TychoRasch/ProjectMask/src/03 Carbon Dioxide Test/Parts/PARTReservoirAssembly.SLDASM

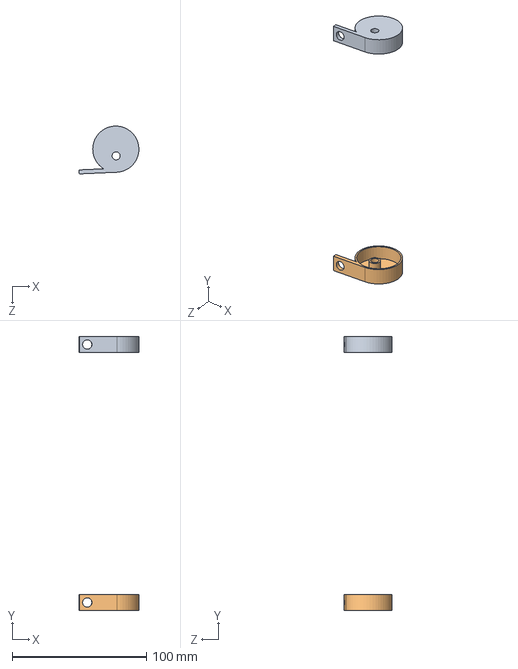
[picture p2: CAD file, 2020-04-27]
src/03 Carbon Dioxide Test/Parts/PARTReservoirAssembly.SLDASM
44.5 x 204.0 x 35.6 mm
PARTReservoirL
PARTReservoirR
