TychoRasch/ProjectMask/src/03 Carbon Dioxide Test/Parts/PARTVenturiAssembly.SLDASM

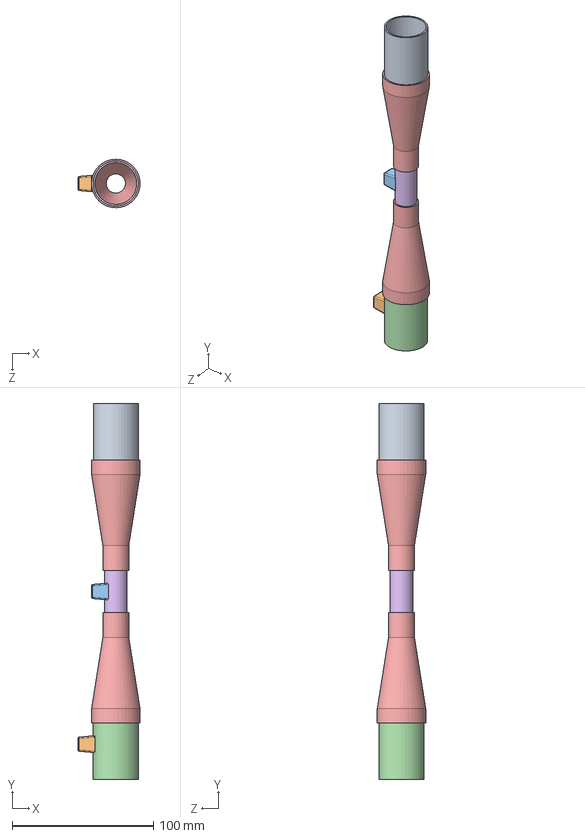
[picture p11: CAD file, 2020-04-27]
src/03 Carbon Dioxide Test/Parts/PARTVenturiAssembly.SLDASM
44.0 x 266.2 x 34.4 mm
PART16mm buis Venturi
PART32-16mm buis Venturi x 2
PART32mm buis Venturi
PART16mm Tube Connect Venturi
PART32mm Tube Connect Venturi
PART32mm buis
