TychoRasch/ProjectMask/src/04 Dry Particle Test/Particle test v1.1/Laser cut files/Baseplate v2.DXF

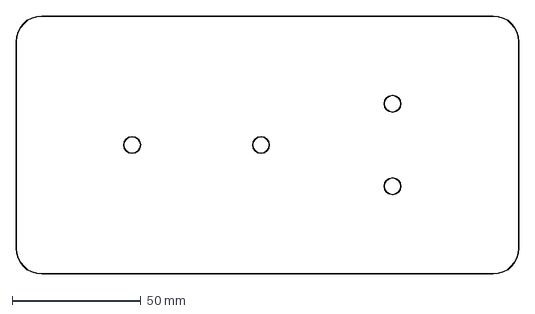
[picture p18: CAD file, 2020-04-27]
src/04 Dry Particle Test/Particle test v1.1/Laser cut files/Baseplate v2.DXF
195.0 x 100.0 mm
