TychoRasch/ProjectMask/src/04 Dry Particle Test/Particle test v1.1/Solidworks model/Baseplate v2.SLDPRT

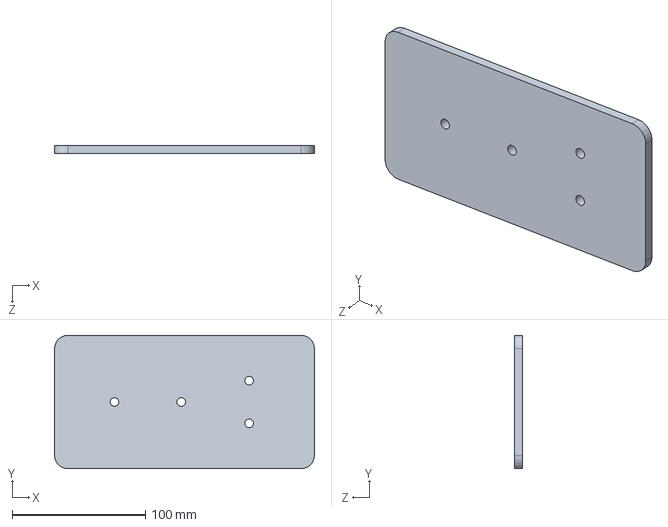
[picture p19: CAD file, 2020-04-27]
src/04 Dry Particle Test/Particle test v1.1/Solidworks model/Baseplate v2.SLDPRT
195.0 x 100.0 x 6.00 mm
