TychoRasch/ProjectMask/src/04 Dry Particle Test/Particle test v1.1/Solidworks model/Particle chamber v3.SLDPRT

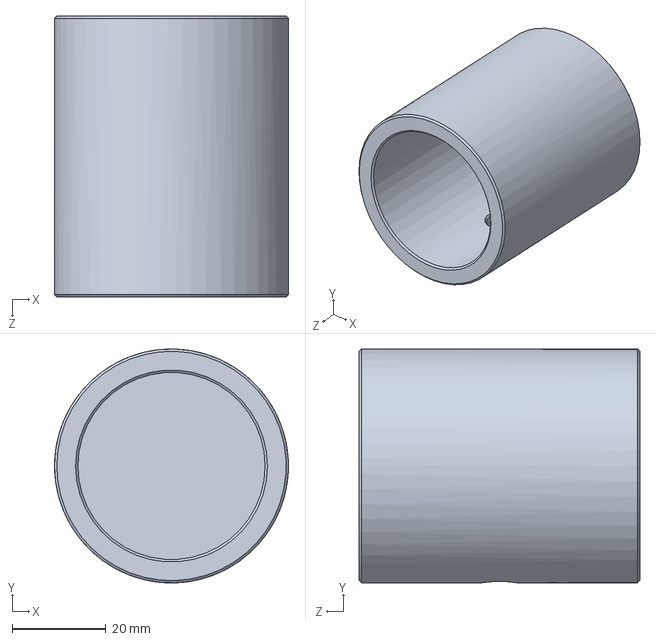
[picture p20: CAD file, 2020-04-27]
src/04 Dry Particle Test/Particle test v1.1/Solidworks model/Particle chamber v3.SLDPRT
50.0 x 50.0 x 60.0 mm
