TychoRasch/ProjectMask/src/03 Carbon Dioxide Test/Parts/PARTMounting1pipe.SLDPRT

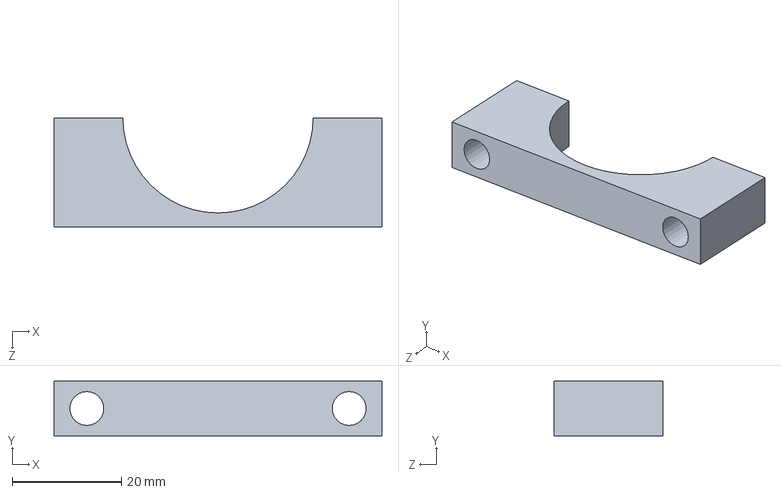
[picture p21: CAD file, 2020-04-27]
src/03 Carbon Dioxide Test/Parts/PARTMounting1pipe.SLDPRT
60.0 x 10.0 x 20.0 mm
