TychoRasch/ProjectMask/src/04 Dry Particle Test/Nebulizer/SolidworksNEN/Feed Tube.SLDPRT

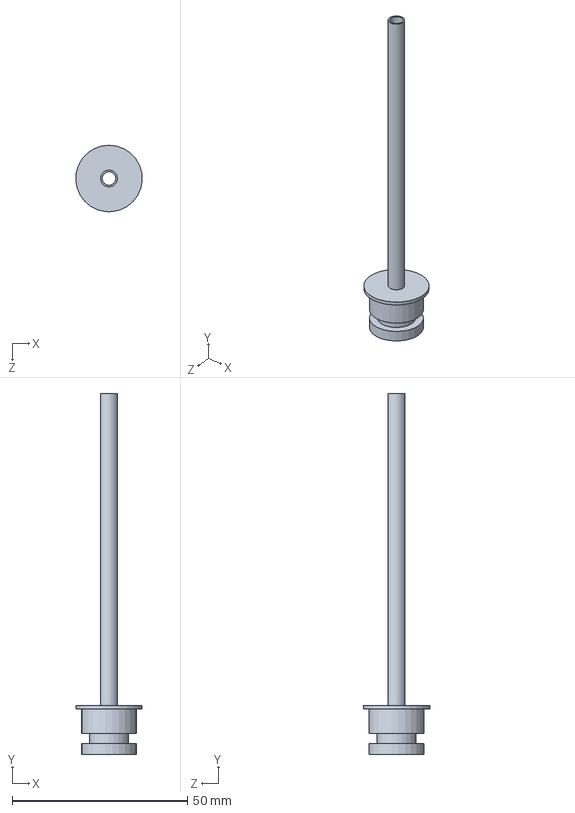
[picture p22: CAD file, 2020-04-27]
src/04 Dry Particle Test/Nebulizer/SolidworksNEN/Feed Tube.SLDPRT
19.0 x 103.0 x 19.0 mm
