TychoRasch/ProjectMask/src/04 Dry Particle Test/Particle test v1.1/Solidworks model/Lid container v3.SLDPRT

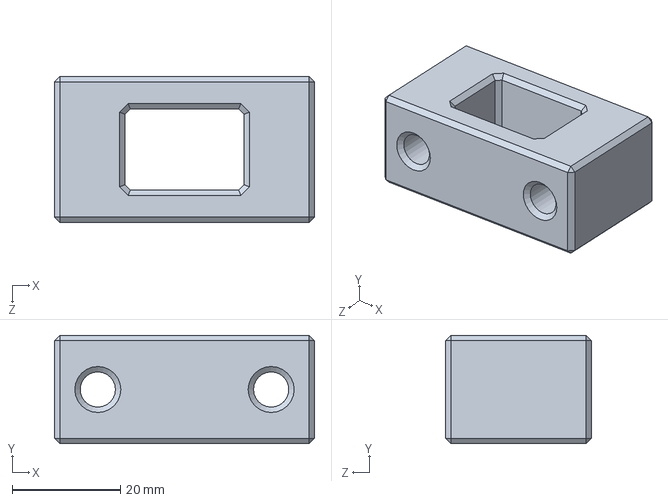
[picture p23: CAD file, 2020-04-27]
src/04 Dry Particle Test/Particle test v1.1/Solidworks model/Lid container v3.SLDPRT
48.0 x 20.0 x 27.0 mm
