TychoRasch/ProjectMask/src/03 Carbon Dioxide Test/Parts/PARTCO2Sensor.SLDPRT

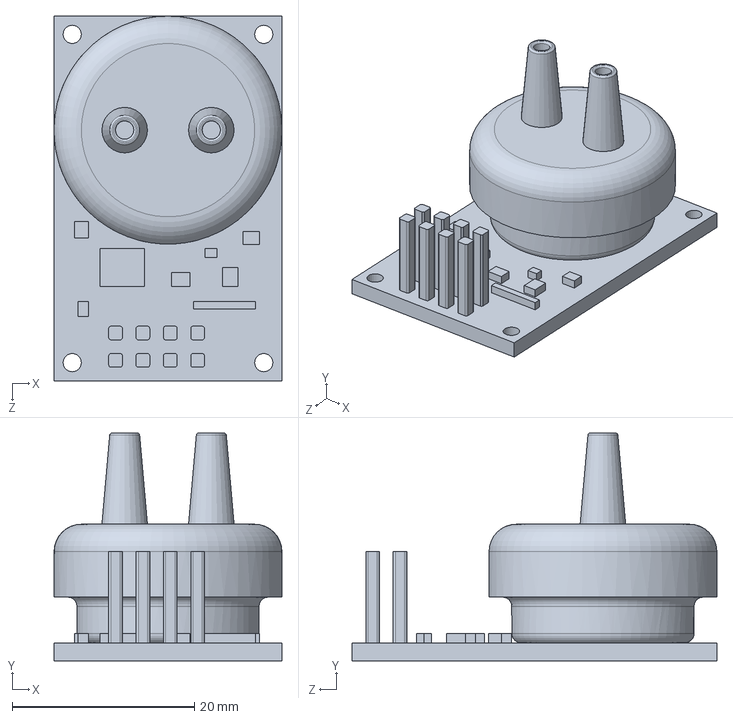
[picture p24: CAD file, 2020-04-27]
src/03 Carbon Dioxide Test/Parts/PARTCO2Sensor.SLDPRT
25.0 x 25.0 x 40.0 mm
