TychoRasch/ProjectMask/src/04 Dry Particle Test/Nebulizer/SolidworksNEN/Plug.SLDPRT

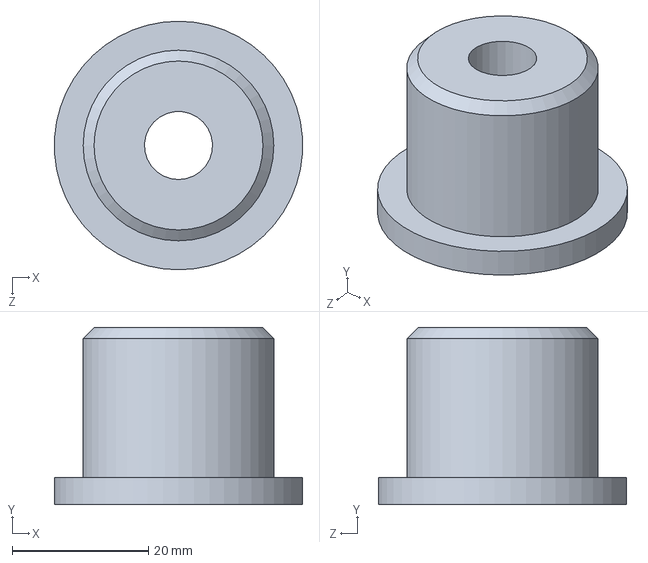
[picture p25: CAD file, 2020-04-27]
src/04 Dry Particle Test/Nebulizer/SolidworksNEN/Plug.SLDPRT
36.4 x 26.0 x 36.5 mm
