TychoRasch/ProjectMask/src/04 Dry Particle Test/Particle test v1.1/Solidworks model/Knob M6.SLDPRT

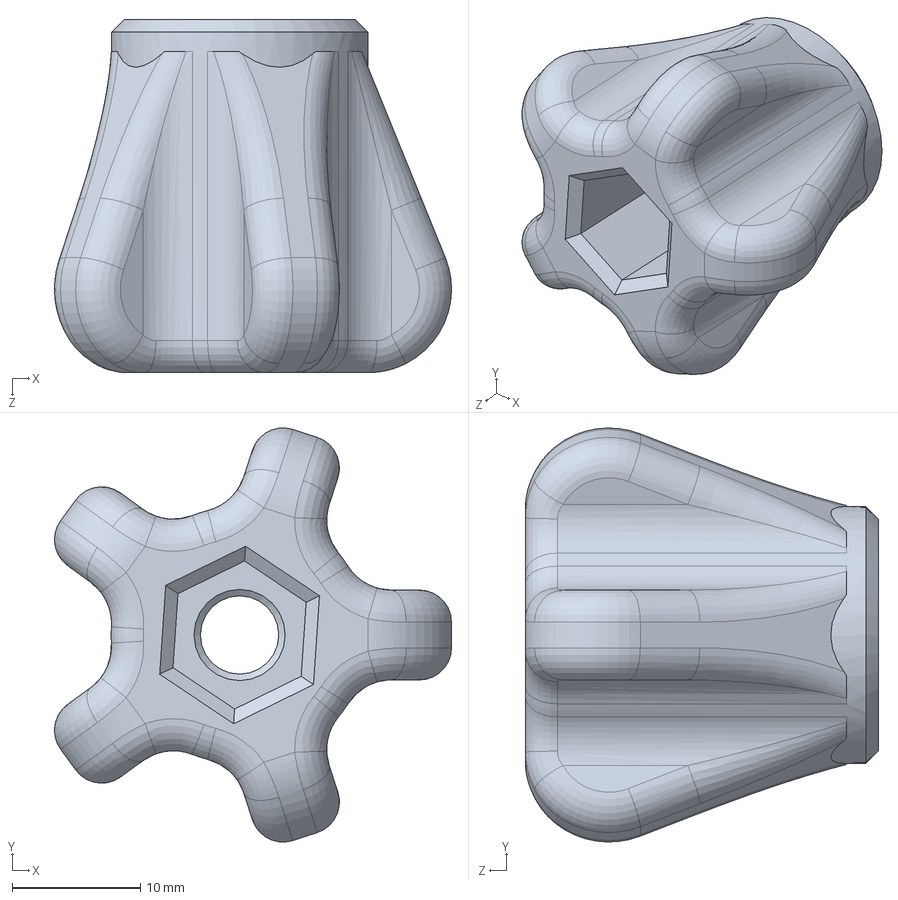
[picture p26: CAD file, 2020-04-27]
src/04 Dry Particle Test/Particle test v1.1/Solidworks model/Knob M6.SLDPRT
30.9 x 32.2 x 27.5 mm
