TychoRasch/ProjectMask/src/04 Dry Particle Test/Particle test v1.1/Solidworks model/Compression lid v2.SLDPRT

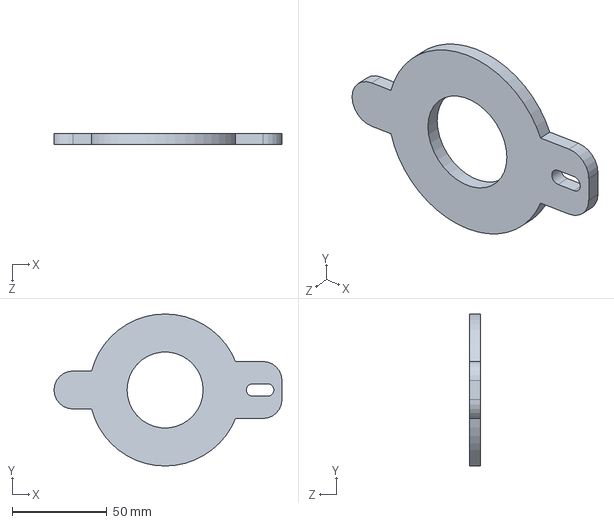
[picture p27: CAD file, 2020-04-27]
src/04 Dry Particle Test/Particle test v1.1/Solidworks model/Compression lid v2.SLDPRT
120.0 x 80.0 x 6.00 mm
