TychoRasch/ProjectMask/src/03 Carbon Dioxide Test/Parts/PARTReservoirR.SLDPRT

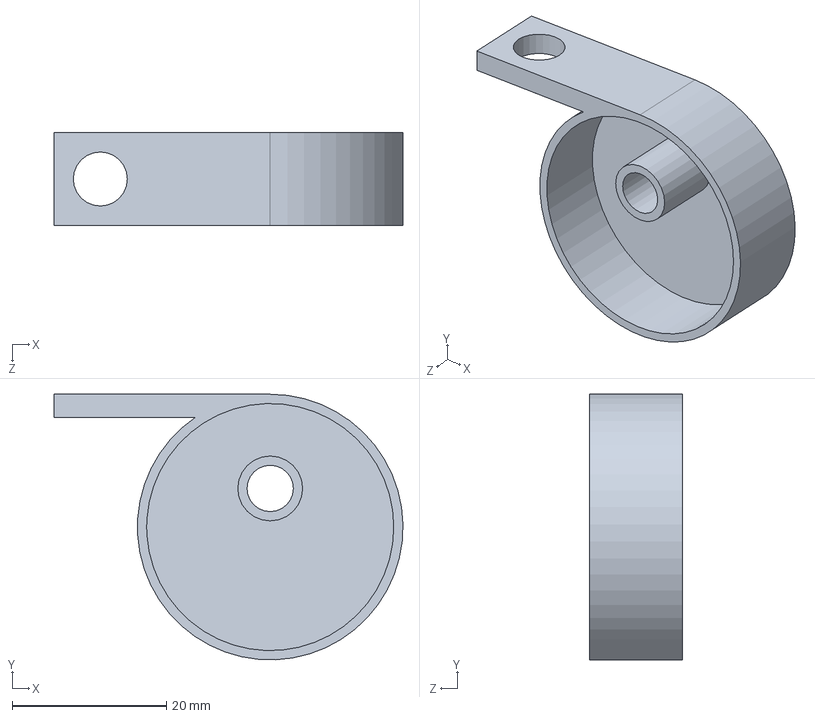
[picture p28: CAD file, 2020-04-27]
src/03 Carbon Dioxide Test/Parts/PARTReservoirR.SLDPRT
45.2 x 34.4 x 12.0 mm
