TychoRasch/ProjectMask/src/04 Dry Particle Test/Particle test v1.1/Solidworks model/Rubber foot.SLDPRT

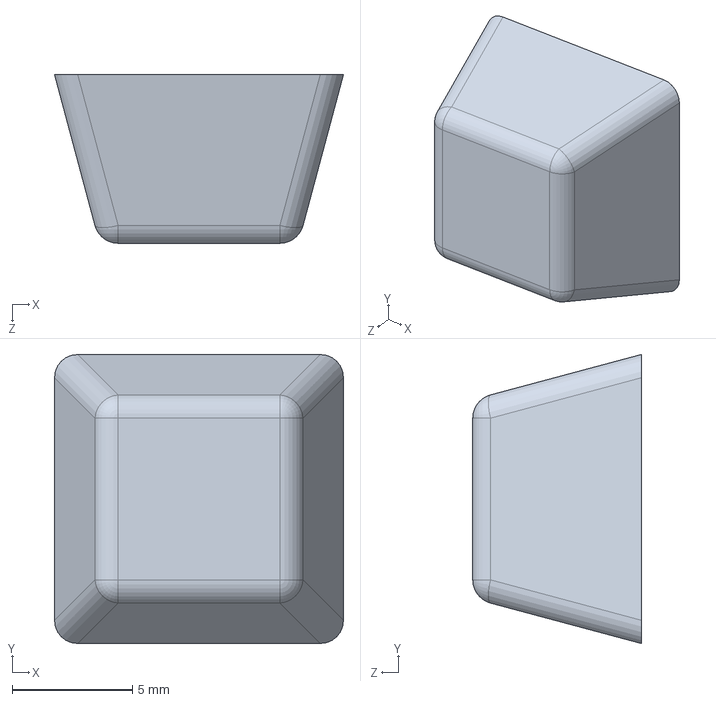
[picture p29: CAD file, 2020-04-27]
src/04 Dry Particle Test/Particle test v1.1/Solidworks model/Rubber foot.SLDPRT
12.0 x 12.0 x 7.00 mm
