TychoRasch/ProjectMask/src/03 Carbon Dioxide Test/Parts/Arduino_Mega_MountV2.SLDPRT

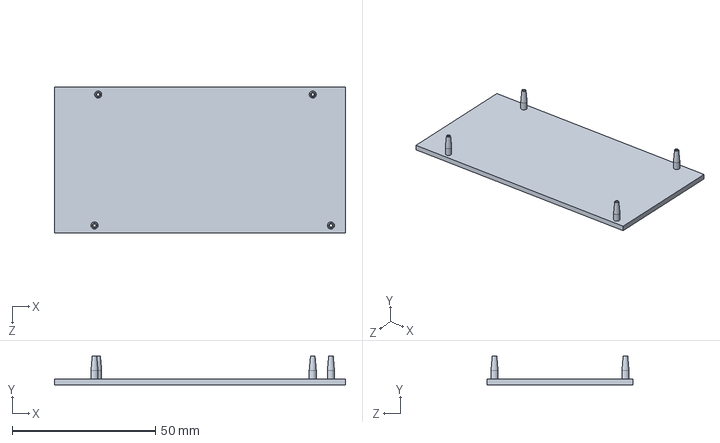
[picture p30: CAD file, 2020-04-27]
src/03 Carbon Dioxide Test/Parts/Arduino_Mega_MountV2.SLDPRT
101.6 x 10.0 x 50.8 mm
