TychoRasch/ProjectMask/src/04 Dry Particle Test/Particle test v1.1/Solidworks model/Seal ring.SLDPRT

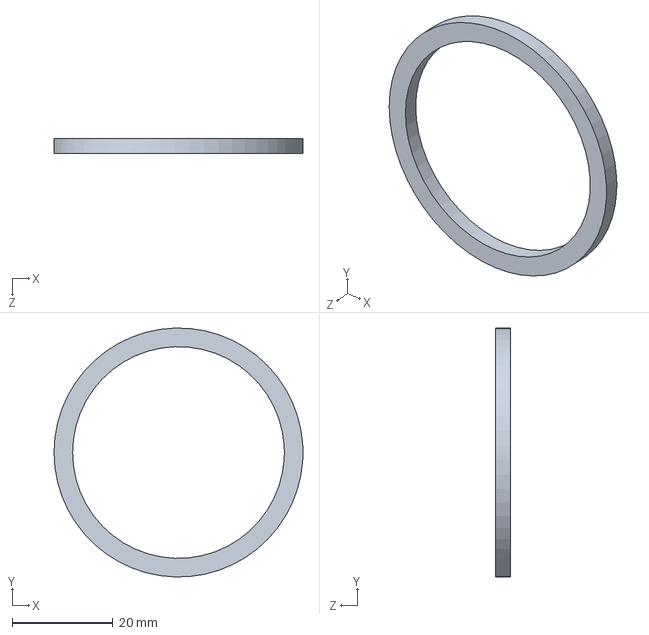
[picture p31: CAD file, 2020-04-27]
src/04 Dry Particle Test/Particle test v1.1/Solidworks model/Seal ring.SLDPRT
49.4 x 49.4 x 3.00 mm
