TychoRasch/ProjectMask/src/03 Carbon Dioxide Test/Parts/PART32-16mm buis Venturi.SLDPRT

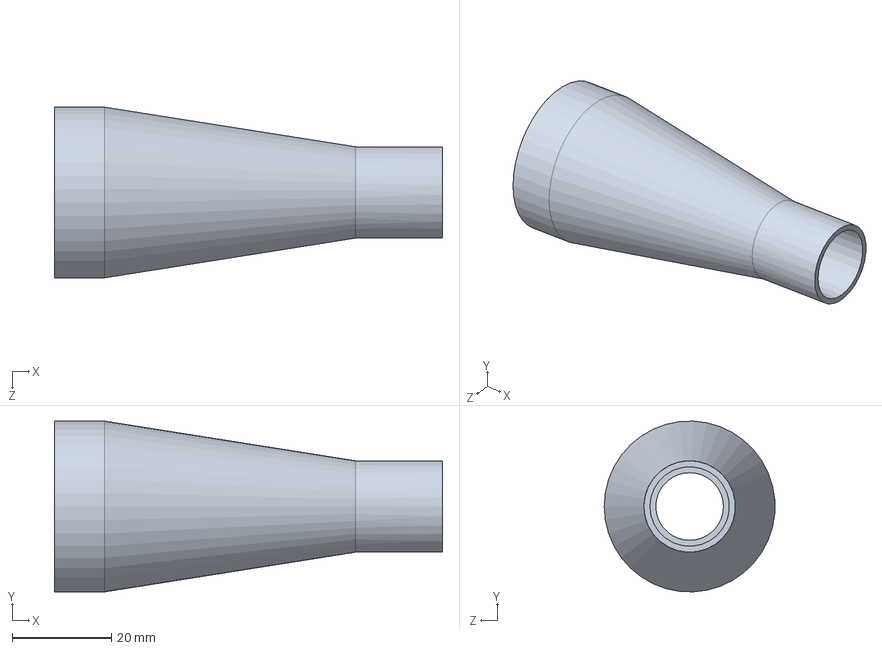
[picture p32: CAD file, 2020-04-27]
src/03 Carbon Dioxide Test/Parts/PART32-16mm buis Venturi.SLDPRT
78.1 x 34.4 x 34.3 mm
