TychoRasch/ProjectMask/src/03 Carbon Dioxide Test/Parts/PARTFanMount.SLDPRT

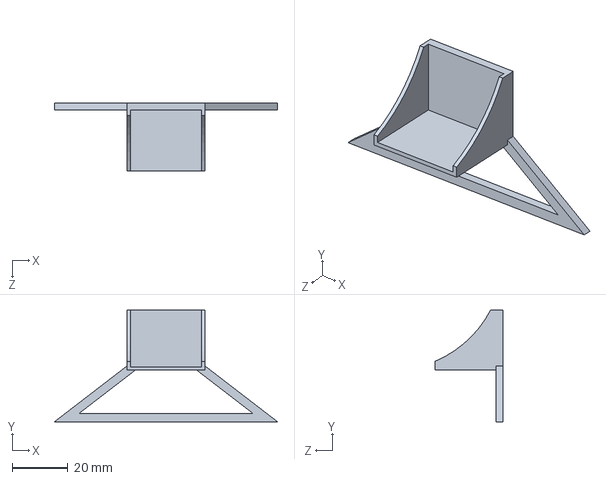
[picture p33: CAD file, 2020-04-27]
src/03 Carbon Dioxide Test/Parts/PARTFanMount.SLDPRT
80.0 x 40.0 x 24.5 mm
