TychoRasch/ProjectMask/src/03 Carbon Dioxide Test/Parts/PARTMounting2pipes.SLDPRT

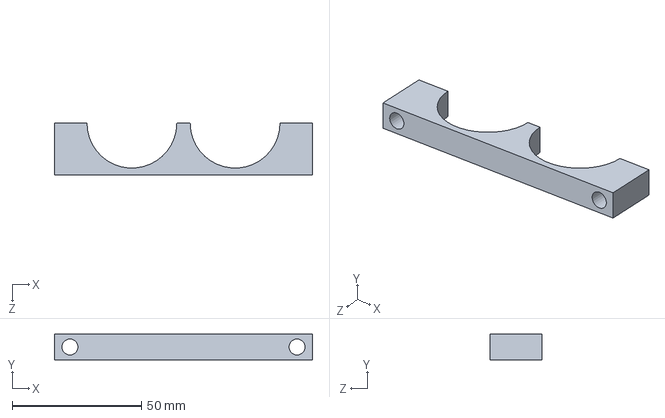
[picture p34: CAD file, 2020-04-27]
src/03 Carbon Dioxide Test/Parts/PARTMounting2pipes.SLDPRT
100.0 x 10.0 x 20.0 mm
