TychoRasch/ProjectMask/src/03 Carbon Dioxide Test/Parts/PART32mm buis TubeConnect.SLDPRT

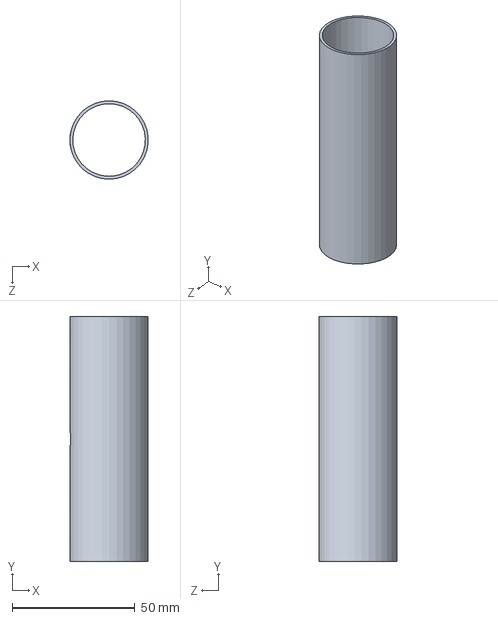
[picture p35: CAD file, 2020-04-27]
src/03 Carbon Dioxide Test/Parts/PART32mm buis TubeConnect.SLDPRT
31.9 x 100.0 x 32.0 mm
