TychoRasch/ProjectMask/src/03 Carbon Dioxide Test/Parts/Arduino_Mega_Mount.SLDPRT

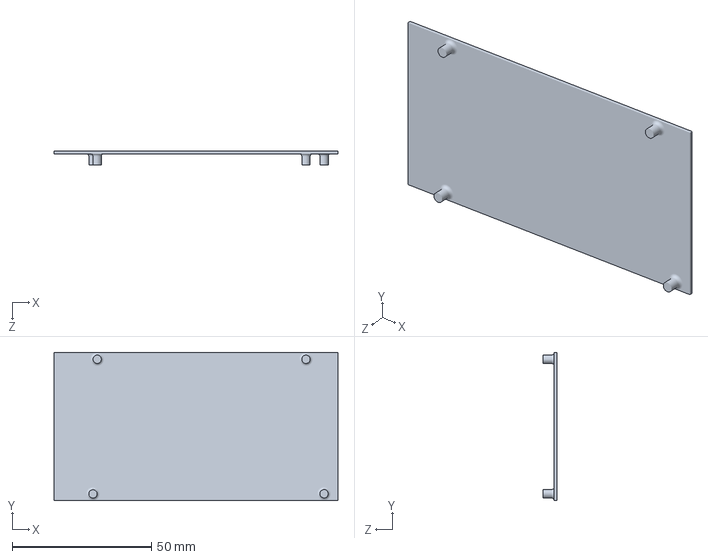
[picture p36: CAD file, 2020-04-27]
src/03 Carbon Dioxide Test/Parts/Arduino_Mega_Mount.SLDPRT
102.0 x 53.3 x 5.00 mm
