TychoRasch/ProjectMask/src/03 Carbon Dioxide Test/Parts/PARTBuildPlateFeet.SLDPRT

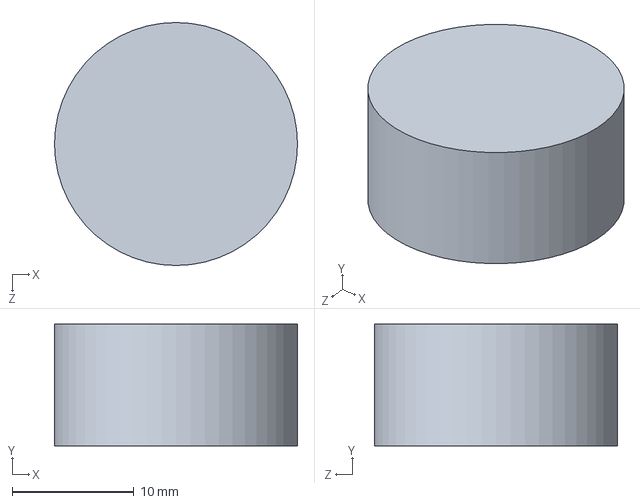
[picture p37: CAD file, 2020-04-27]
src/03 Carbon Dioxide Test/Parts/PARTBuildPlateFeet.SLDPRT
20.0 x 10.0 x 20.0 mm
