TychoRasch/ProjectMask/src/03 Carbon Dioxide Test/Parts/PART32mm buis Venturi.SLDPRT

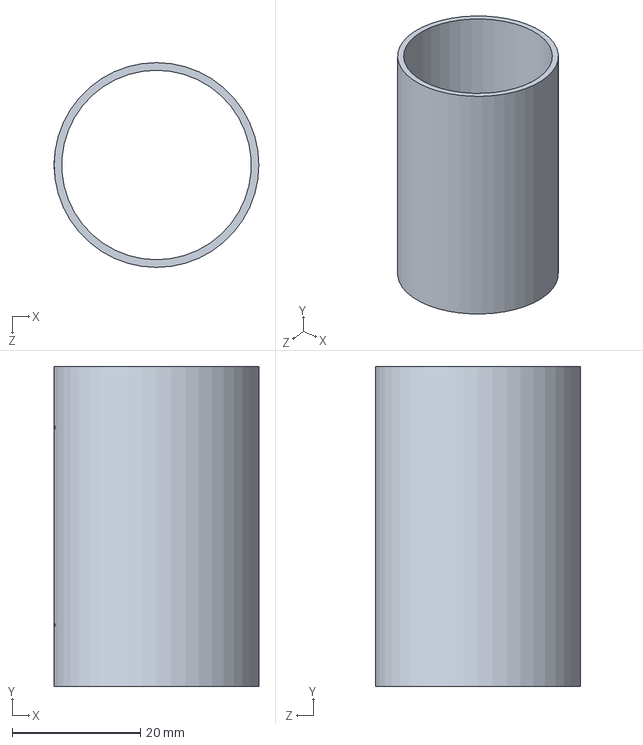
[picture p38: CAD file, 2020-04-27]
src/03 Carbon Dioxide Test/Parts/PART32mm buis Venturi.SLDPRT
32.0 x 50.0 x 32.0 mm
