TychoRasch/ProjectMask/src/03 Carbon Dioxide Test/Parts/PART32mm Tube Connect Venturi.SLDPRT

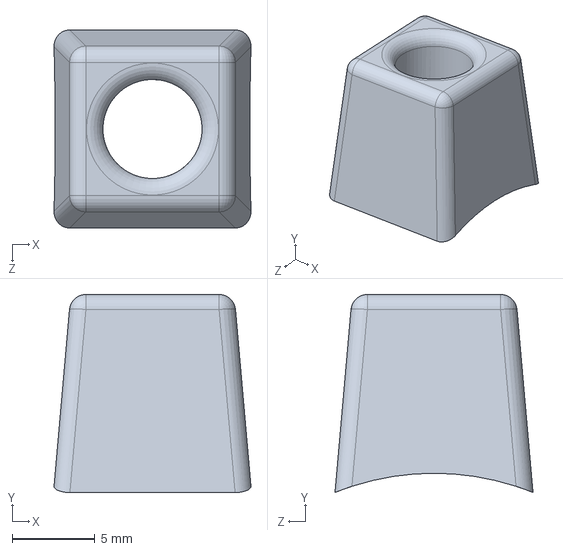
[picture p39: CAD file, 2020-04-27]
src/03 Carbon Dioxide Test/Parts/PART32mm Tube Connect Venturi.SLDPRT
11.9 x 12.0 x 12.0 mm
