TychoRasch/ProjectMask/src/03 Carbon Dioxide Test/Parts/PART16mm Tube Connect Venturi.SLDPRT

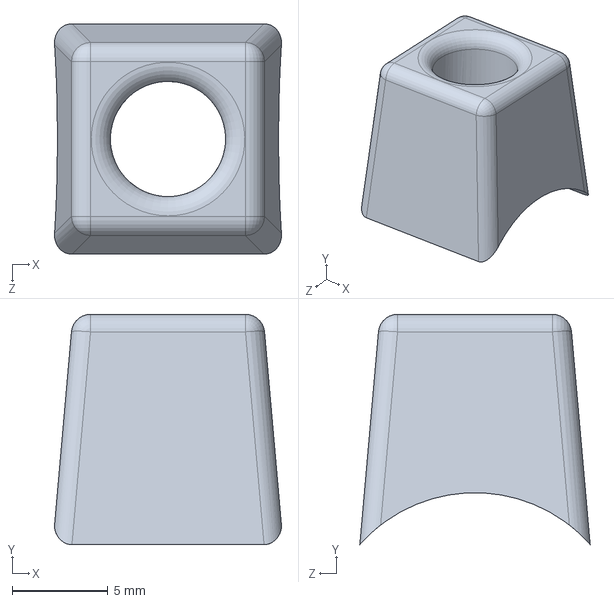
[picture p40: CAD file, 2020-04-27]
src/03 Carbon Dioxide Test/Parts/PART16mm Tube Connect Venturi.SLDPRT
11.8 x 12.0 x 12.0 mm
