TychoRasch/ProjectMask/src/03 Carbon Dioxide Test/Parts/PARTPressureSensor.SLDPRT

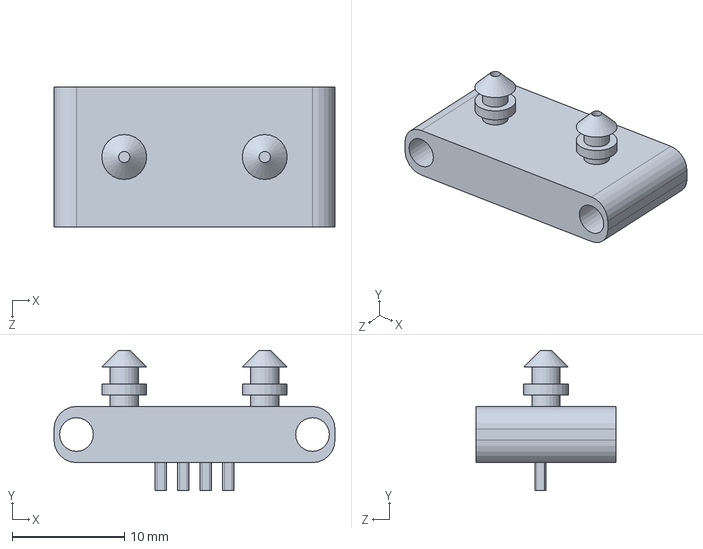
[picture p41: CAD file, 2020-04-27]
src/03 Carbon Dioxide Test/Parts/PARTPressureSensor.SLDPRT
25.0 x 12.5 x 12.5 mm
