TychoRasch/ProjectMask/src/03 Carbon Dioxide Test/Parts/PART80MM_FAN.step.SLDPRT

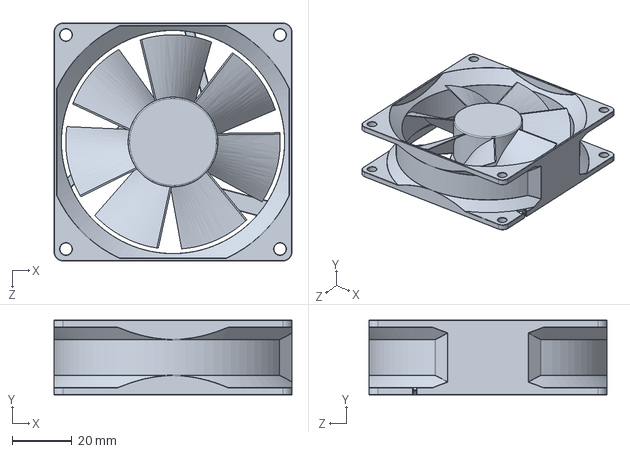
[picture p42: CAD file, 2020-04-27]
src/03 Carbon Dioxide Test/Parts/PART80MM_FAN.step.SLDPRT
79.5 x 25.0 x 79.5 mm
