TychoRasch/ProjectMask/src/03 Carbon Dioxide Test/Parts/PARTMouthPiece.SLDPRT

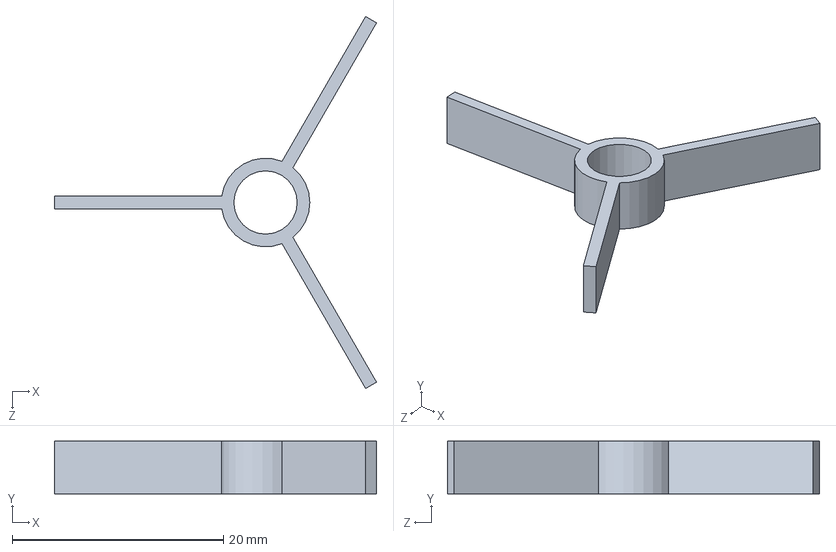
[picture p43: CAD file, 2020-04-27]
src/03 Carbon Dioxide Test/Parts/PARTMouthPiece.SLDPRT
30.5 x 5.00 x 35.2 mm
