TychoRasch/ProjectMask/src/03 Carbon Dioxide Test/Parts/PART16mm buis Venturi.SLDPRT

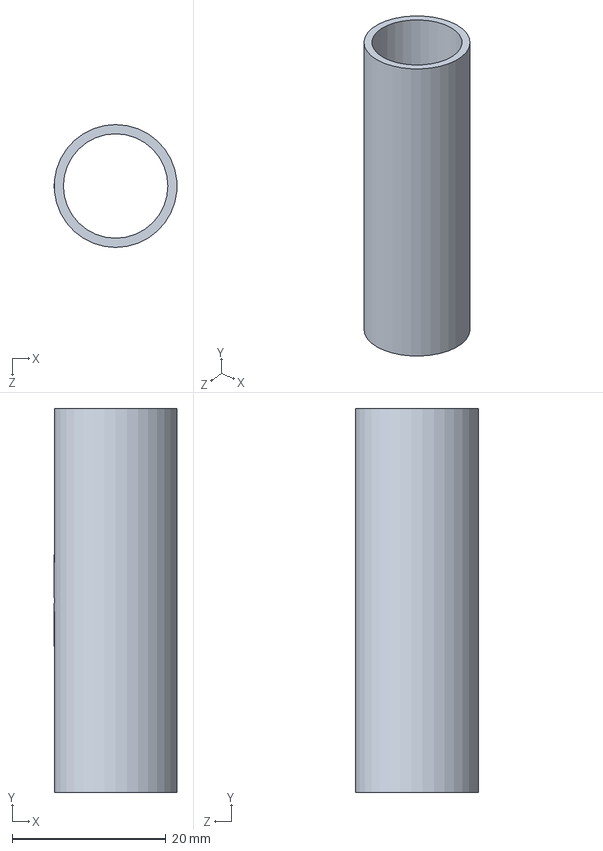
[picture p44: CAD file, 2020-04-27]
src/03 Carbon Dioxide Test/Parts/PART16mm buis Venturi.SLDPRT
16.0 x 50.0 x 16.0 mm
