TychoRasch/ProjectMask/src/03 Carbon Dioxide Test/Parts/PART32mm buis Reservoir.SLDPRT

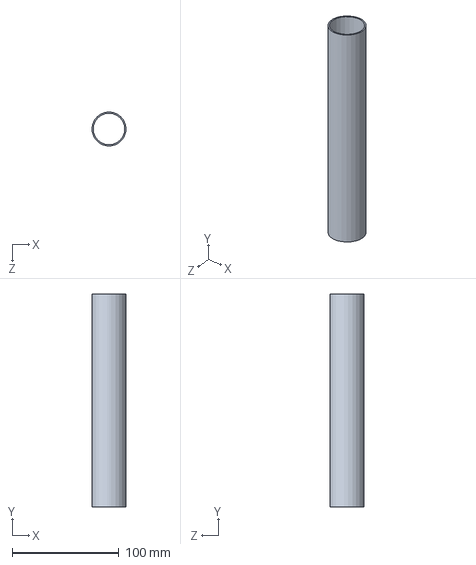
[picture p45: CAD file, 2020-04-27]
src/03 Carbon Dioxide Test/Parts/PART32mm buis Reservoir.SLDPRT
31.9 x 200.0 x 32.0 mm
